LeBellier/LEDTable/Electronique/Modeling/WemosSize.jpg

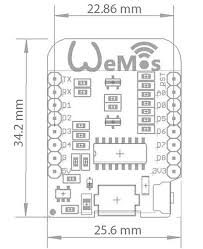
Electronique/Modeling/WemosSize.jpg
