LeBellier/LEDTable/Photos/2016-08-09 19.20.28.jpg

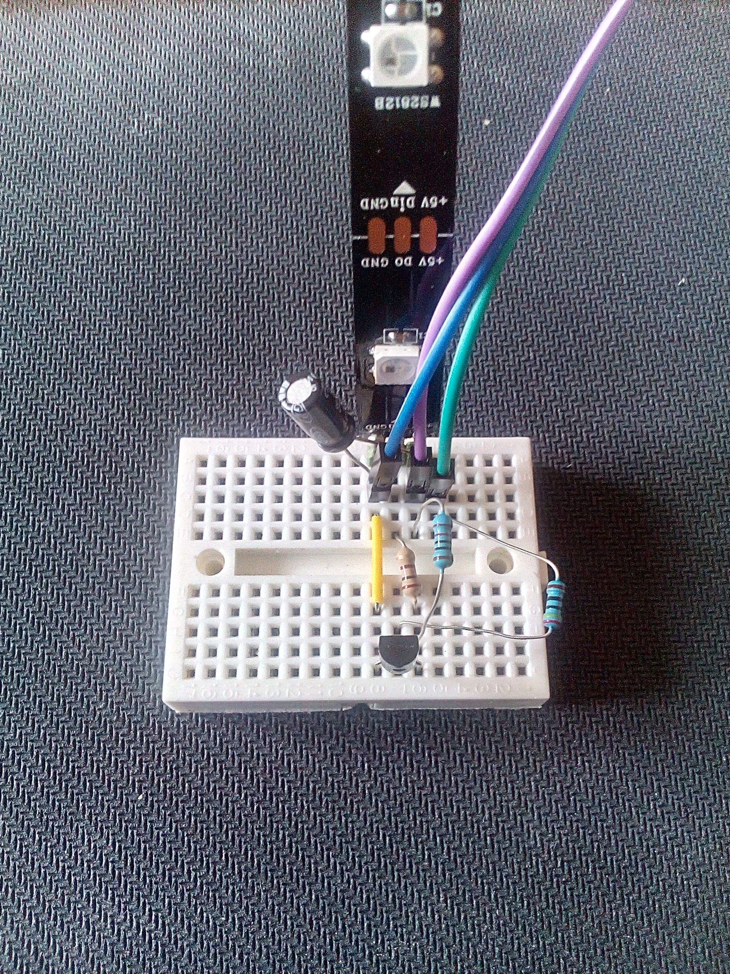
Photos/2016-08-09 19.20.28.jpg
