LeBellier/LEDTable/Photos/2016-08-09 19.20.53.jpg

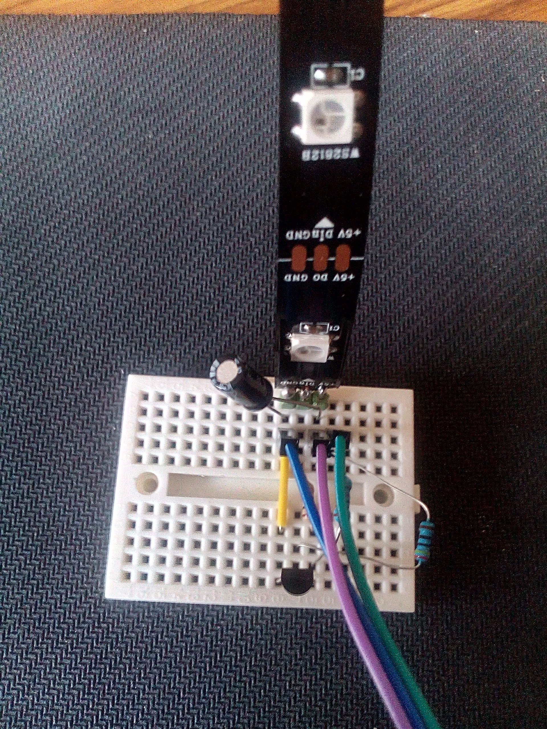
Photos/2016-08-09 19.20.53.jpg
