LeBellier/LEDTable/Photos/2016-09-05 17.38.15 Last.jpg

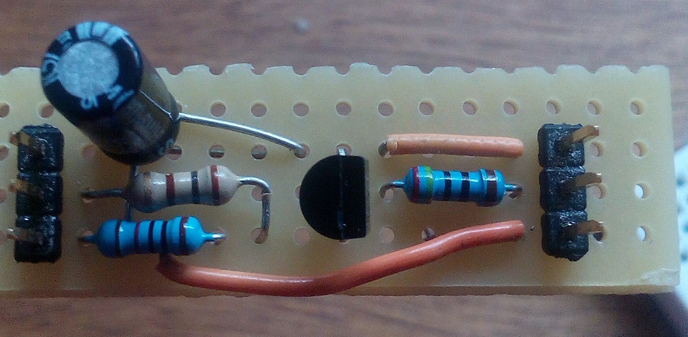
Photos/2016-09-05 17.38.15 Last.jpg
