LeBellier/LEDTable/Photos/2016-09-08 schem.png

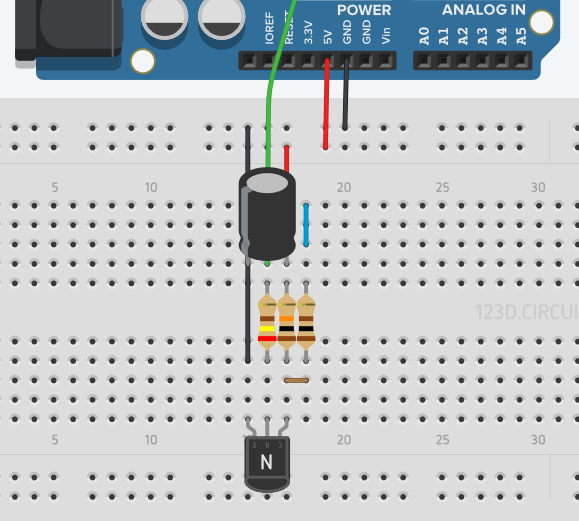
Photos/2016-09-08 schem.png
