LeBellier/LEDTable/Photos/2016-09-18 16.33.44.jpg

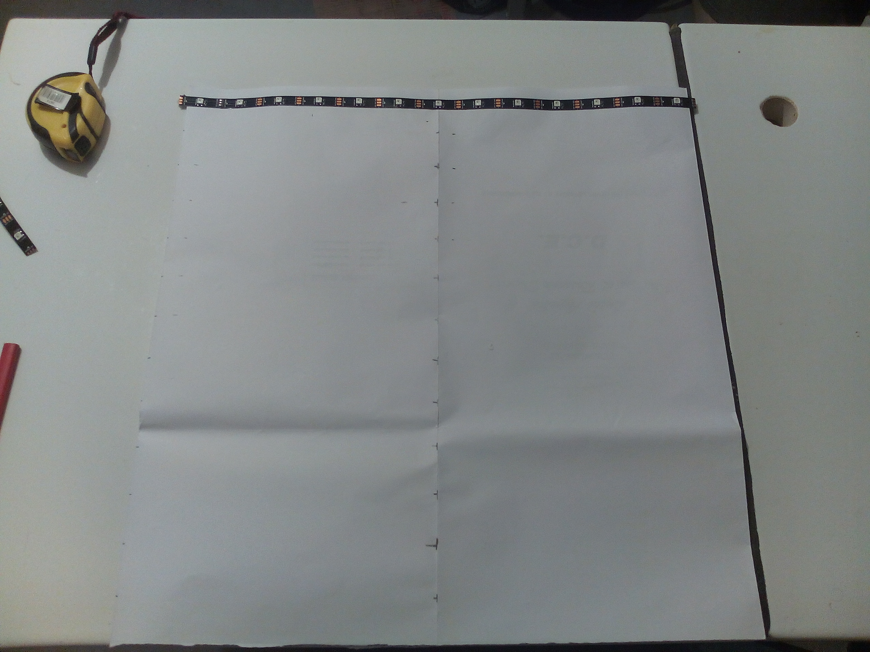
Photos/2016-09-18 16.33.44.jpg
