LeBellier/LEDTable/Photos/2016-09-18 17.44.51.jpg

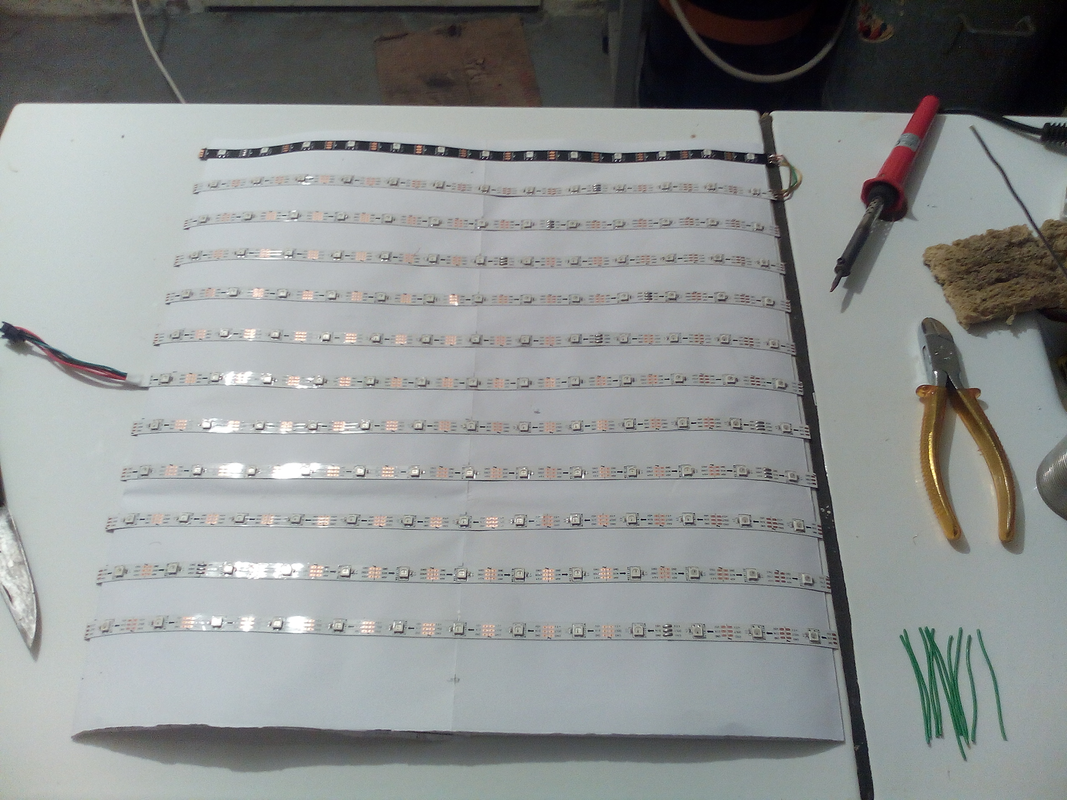
Photos/2016-09-18 17.44.51.jpg
