LeBellier/LEDTable/Photos/2016-09-18 17.50.01.jpg

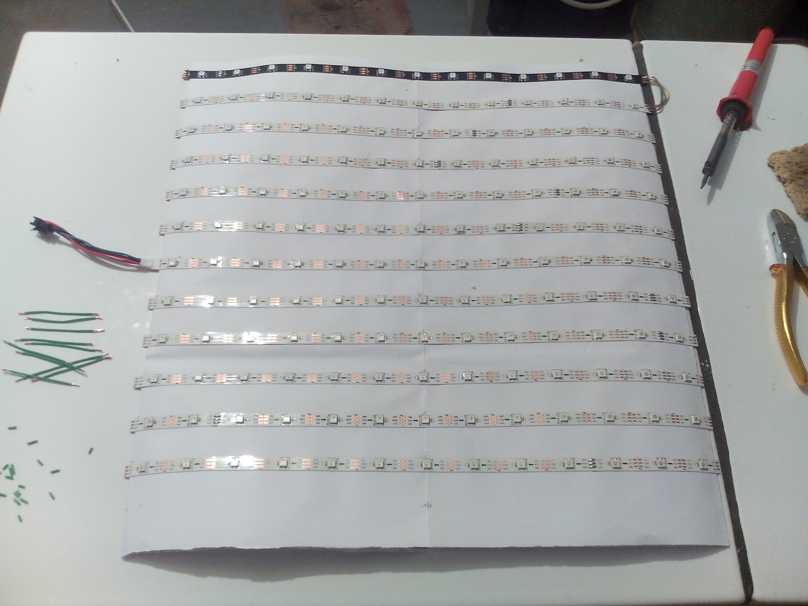
Photos/2016-09-18 17.50.01.jpg
