LeBellier/LEDTable/Photos/2016-09-18 18.18.31.jpg

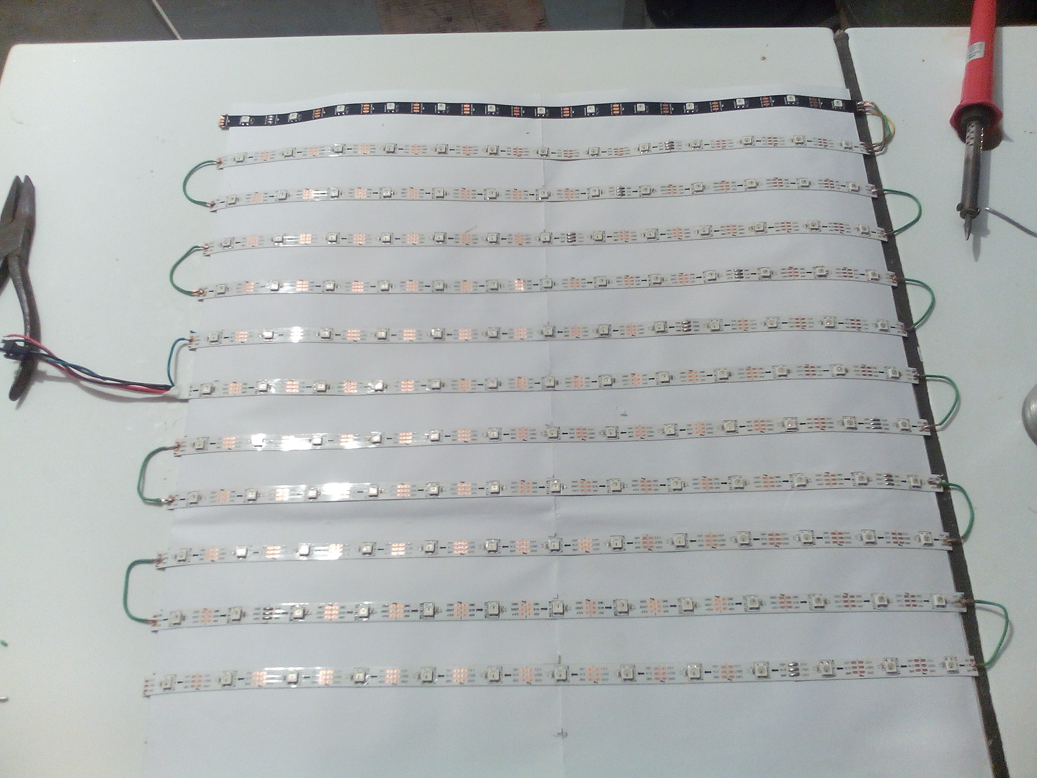
Photos/2016-09-18 18.18.31.jpg
