LeBellier/LEDTable/Photos/2016-09-18 19.18.12.jpg

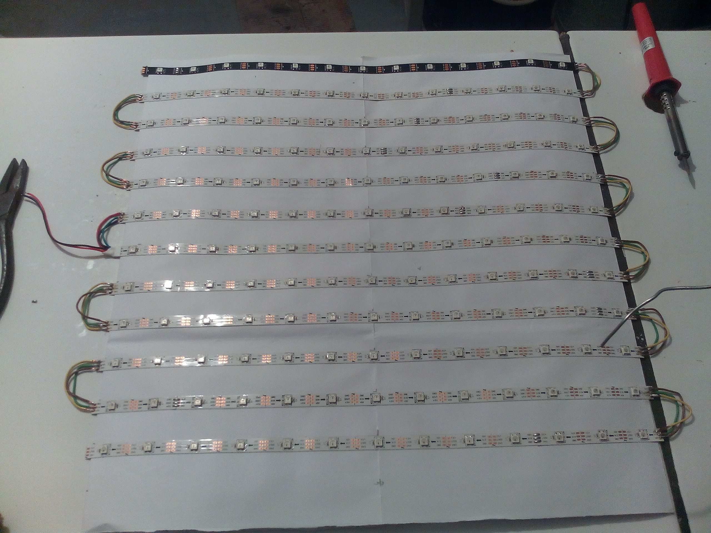
Photos/2016-09-18 19.18.12.jpg
