LeBellier/LEDTable/Photos/2016-09-18 19.18.13.jpg

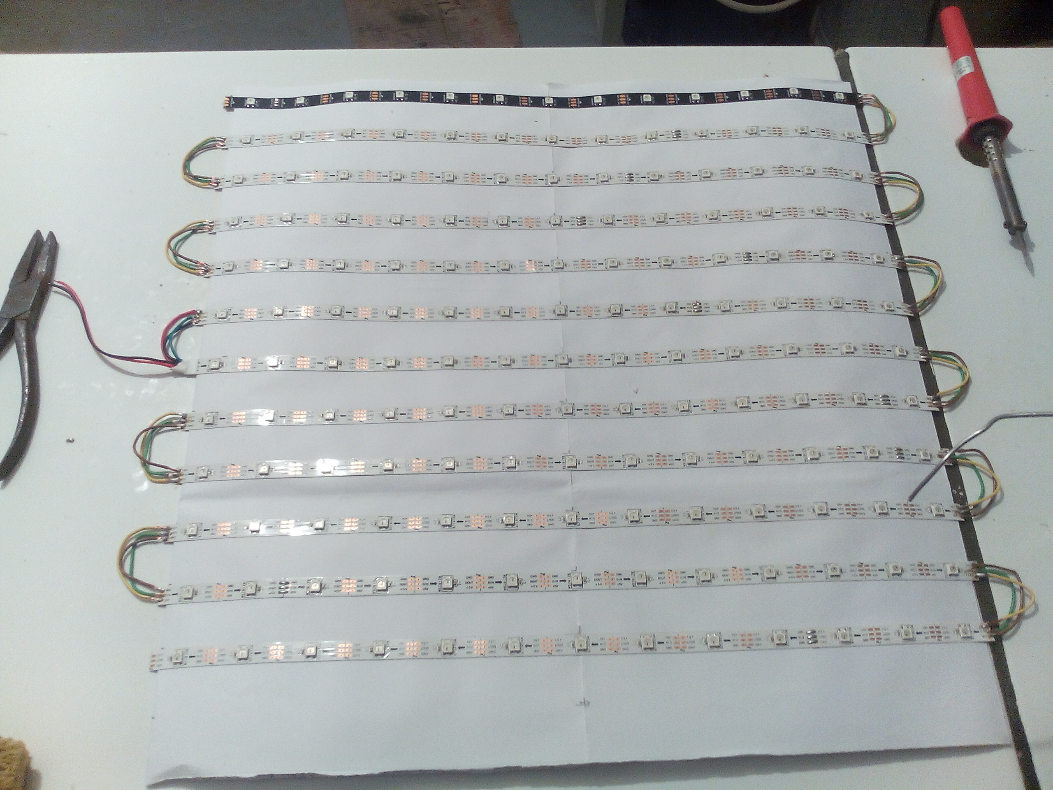
Photos/2016-09-18 19.18.13.jpg
