LeBellier/LEDTable/Photos/2016-09-18 19.37.42.jpg

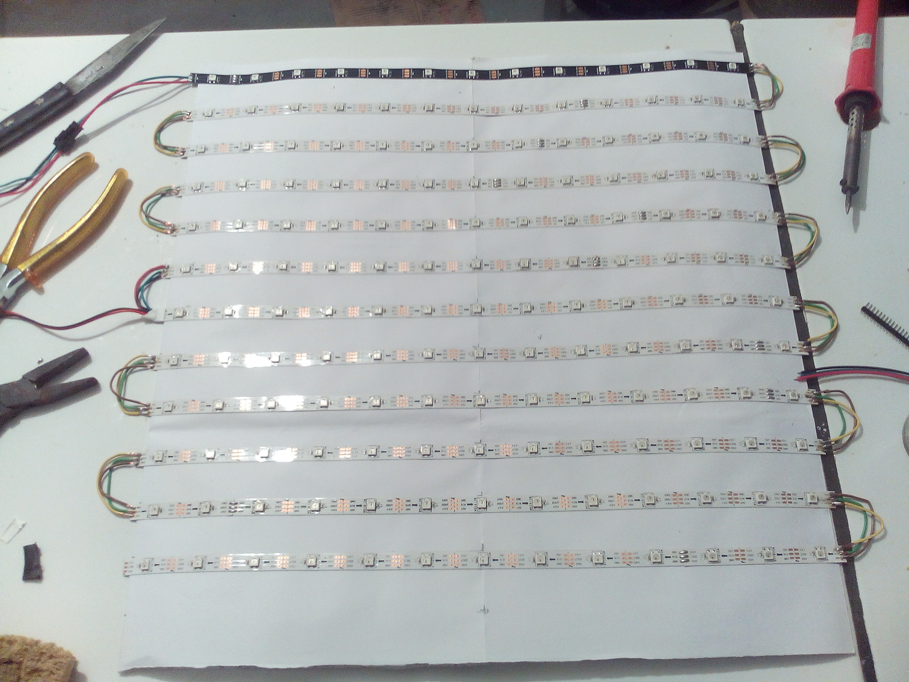
Photos/2016-09-18 19.37.42.jpg
