LeBellier/LEDTable/Photos/2016-09-19 10.16.02.jpg

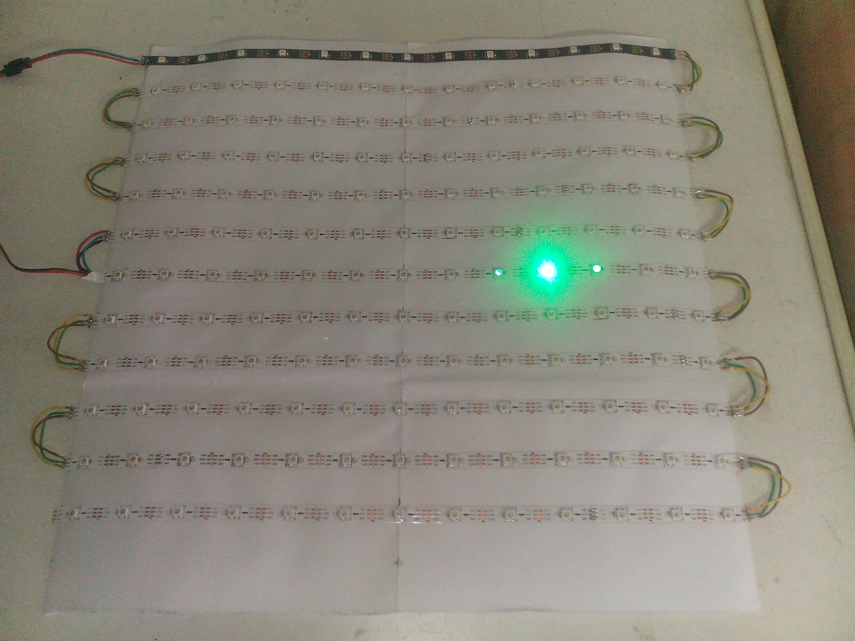
Photos/2016-09-19 10.16.02.jpg
