LeBellier/LEDTable/Photos/2016-09-22 15.28.25.jpg

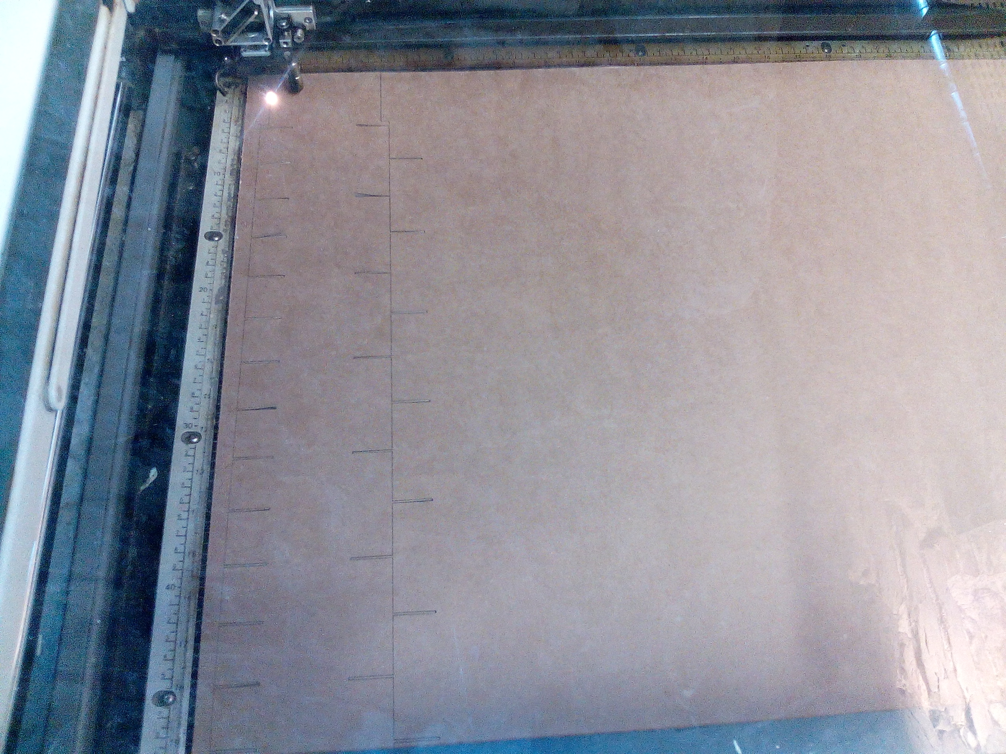
Photos/2016-09-22 15.28.25.jpg
