LeBellier/LEDTable/Photos/2016-09-22 15.30.50.jpg

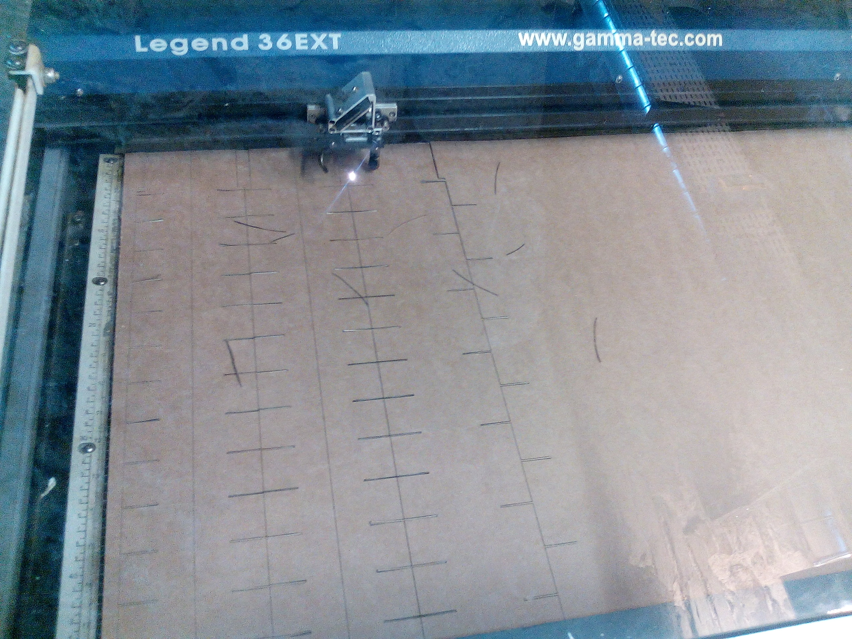
Photos/2016-09-22 15.30.50.jpg
