LeBellier/LEDTable/Photos/2016-09-26 12.01.59.jpg

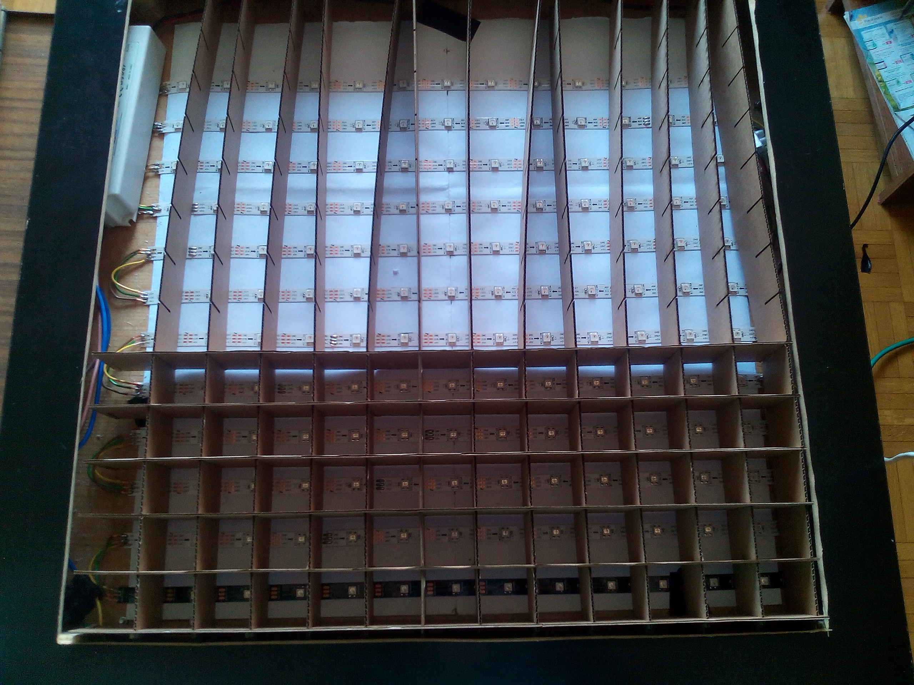
Photos/2016-09-26 12.01.59.jpg
