LeBellier/LEDTable/Photos/2016-09-26 12.21.53.jpg

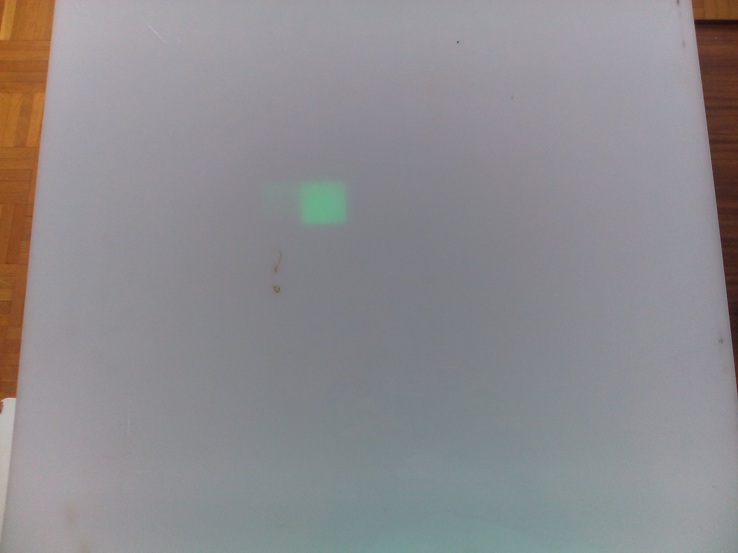
Photos/2016-09-26 12.21.53.jpg
