LeBellier/LEDTable/Photos/2016-09-26 15.10.22.jpg

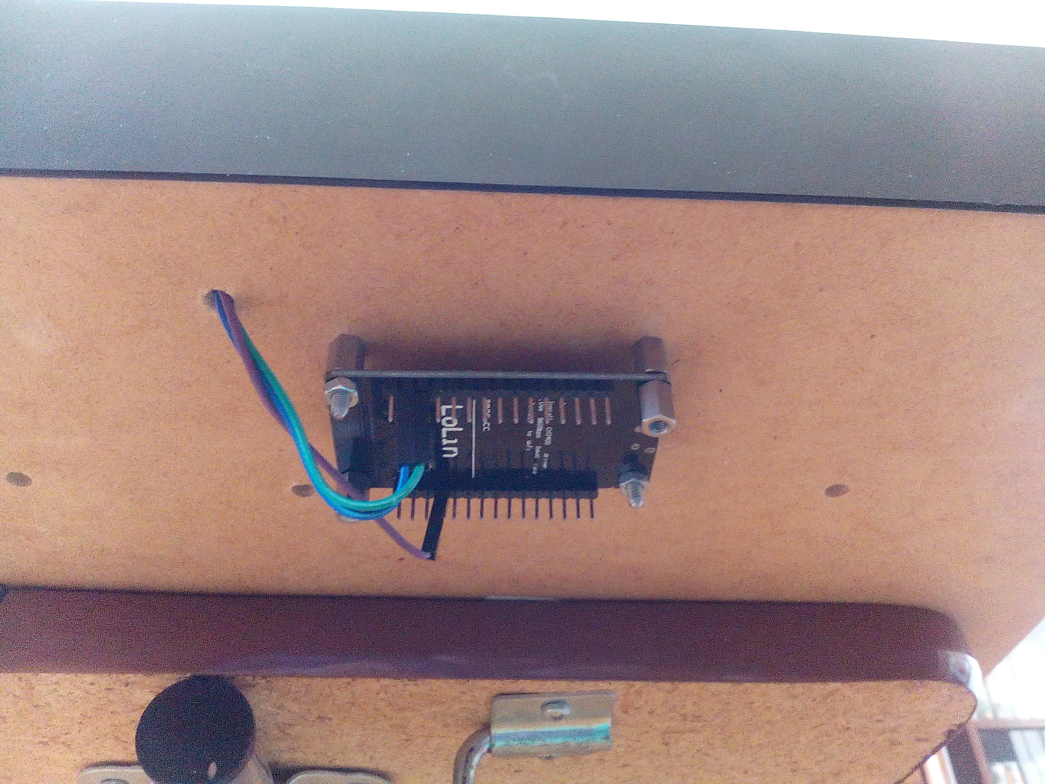
Photos/2016-09-26 15.10.22.jpg
