LeBellier/LEDTable/Photos/2016-10-25 10.06.50.jpg

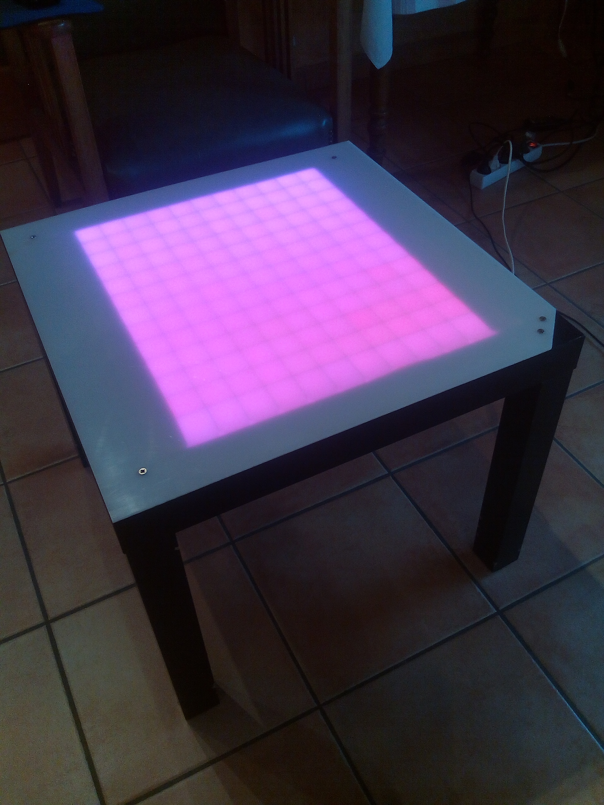
Photos/2016-10-25 10.06.50.jpg
