LeBellier/LEDTable/CodeArduino/TableALed/include/CharAndColor.h

// CharAndColor.h

#ifndef _CHARANDCOLOR_h
#define _CHARANDCOLOR_h

//Define the "Normal" 32 bit colors
static const uint32_t BLACK = 0;
static const uint32_t RED = 0xFF << 16;
static const uint32_t GREEN = 0xFF << 8;
static const uint32_t BLUE = 0xFF;
static const uint32_t ORANGE = RED | GREEN;
static const uint32_t MAGENTA = RED | BLUE;
static const uint32_t TEAL = BLUE | GREEN;
static const uint32_t WHITE = (RED | GREEN | BLUE);

//Chars
//8x8 font.
const char letters[] = { 0x00, 0x00, 0x00, 0x00, 0x00, 0x00, 0x00, 0x00, //0/ --> ' '
0x00, 0x7E, 0x11, 0x11, 0x11, 0x7E, 0x00, 0x00, //65/ --> A
0x00, 0x7F, 0x49, 0x49, 0x49, 0x36, 0x00, 0x00, //66/ --> B
0x00, 0x3E, 0x41, 0x41, 0x41, 0x22, 0x00, 0x00, //67/ --> C
0x00, 0x7F, 0x41, 0x41, 0x22, 0x1C, 0x00, 0x00, //68/ --> D
0x00, 0x7F, 0x49, 0x49, 0x49, 0x41, 0x00, 0x00, //69/ --> E
0x00, 0x7F, 0x09, 0x09, 0x09, 0x01, 0x00, 0x00, //70/ --> F
0x00, 0x3E, 0x41, 0x49, 0x49, 0x3A, 0x00, 0x00, //71/ --> G
0x00, 0x7F, 0x08, 0x08, 0x08, 0x7F, 0x00, 0x00, //72/ --> H
0x00, 0x00, 0x41, 0x7F, 0x41, 0x00, 0x00, 0x00, //73/ --> I
0x00, 0x20, 0x40, 0x41, 0x3F, 0x01, 0x00, 0x00, //74/ --> J
0x00, 0x7F, 0x08, 0x14, 0x22, 0x41, 0x00, 0x00, //75/ --> K
0x00, 0x7F, 0x40, 0x40, 0x40, 0x40, 0x00, 0x00, //76/ --> L
0x00, 0x7F, 0x02, 0x0C, 0x02, 0x7F, 0x00, 0x00, //77/ --> M
0x00, 0x7F, 0x04, 0x08, 0x10, 0x7F, 0x00, 0x00, //78/ --> N
0x00, 0x3E, 0x41, 0x41, 0x41, 0x3E, 0x00, 0x00, //79/ --> O
0x00, 0x7F, 0x09, 0x09, 0x09, 0x06, 0x00, 0x00, //80/ --> P
0x3E, 0x41, 0x51, 0x21, 0x5E, 0x00, 0x00, 0x00, //81/ --> Q
0x00, 0x7F, 0x09, 0x19, 0x29, 0x46, 0x00, 0x00, //82/ --> R
0x00, 0x46, 0x49, 0x49, 0x49, 0x31, 0x00, 0x00, //83/ --> S
0x00, 0x01, 0x01, 0x7F, 0x01, 0x01, 0x00, 0x00, //84/ --> T
0x00, 0x3F, 0x40, 0x40, 0x40, 0x3F, 0x00, 0x00, //85/ --> U
0x00, 0x1F, 0x20, 0x40, 0x20, 0x1F, 0x00, 0x00, //86/ --> V
0x00, 0x3F, 0x40, 0x70, 0x40, 0x3F, 0x00, 0x00, //87/ --> W
0x00, 0x63, 0x14, 0x08, 0x14, 0x63, 0x00, 0x00, //88/ --> X
0x00, 0x07, 0x08, 0x70, 0x08, 0x07, 0x00, 0x00, //89/ --> Y
0x00, 0x61, 0x51, 0x49, 0x45, 0x43, 0x00, 0x00, //90/ --> Z
};
//Font 3*6
const char numbers[] = { 0x00, 0x00, 0x00, //0 -->" "
0x1F, 0x11, 0x1F, //48-->0
0x00, 0x1F, 0x00, //49-->1
0x17, 0x15, 0x1D, //50-->2
0x11, 0x15, 0x1F, //51-->3
0x1E, 0x02, 0x07, //52-->4
0x1D, 0x15, 0x17, //53-->5
0x1F, 0x15, 0x07, //54-->6
0x10, 0x10, 0x1F, //55-->7
0x1F, 0x15, 0x1F, //56-->8
0x1C, 0x15, 0x1F //57-->9
};
#endif
