LeBellier/LEDTable/CodeArduino/TableALed/include/GlobalVars.h

#ifndef GLOBALVARS_H
#define GLOBALVARS_H

// Debug Speed
#define BAUDRATE 115200

// Pins and HardWare
#define pixelPin D3
#define led D4
uint8_t nbRows = 12;
uint8_t nbColumns = 13;

// Globals Object
ArtnetWifi artnet;


//Page de commentaires divers

/*#define D0   16
#define D1   5
#define D2   4
#define D3   0
#define D4   2 // builtin LED
#define D5   14
#define D6   12
#define D7   13
#define D8   15
#define D9   3
#define D10  1
*/

#endif
