LeBellier/LEDTable/CodeArduino/TableALed/include/TAL.h

/*
* tal.h
*
*  Created on: 5 sept. 2017
*      Author: Bruno
*/

#ifndef TAL_H_
#define TAL_H_

#include <ArduinoOTA.h>
#include <WiFiUdp.h>
#include <WiFiServer.h>
#include <WiFiClientSecure.h>
#include <WiFiClient.h>
#include <ESP8266WiFiType.h>
#include <ESP8266WiFiSTA.h>
#include <ESP8266WiFiScan.h>
#include <ESP8266WiFiMulti.h>
#include <ESP8266WiFiGeneric.h>
#include <ESP8266WiFiAP.h>
#include <ESP8266WiFi.h>
#include <DNSServer.h>
#include <ESP8266WebServer.h>

#include <Adafruit_NeoPixel.h>
#include "MatrixStrip.h"
#include "ServerManager.h"
#include "WifiManager.h"

#include <ESP8266WebServer.h>
#include "MatrixStrip.h"
#include "ESP8266TelnetServer.h"
#include "ServerManager.h"
#include "WifiManager.h"
#include <ArtnetWifi.h>

#include "GlobalVars.h"

#include "Animations.h" // besoin de IPAdress
#include "Callbacks.h"	// besoin du strip

#endif /* TAL_H_ */
