LeBellier/LEDTable/CodeArduino/FTPServerSample/FTPServerSample.ino

#include <ESP8266WiFi.h>          //https://github.com/esp8266/Arduino

//needed for library
#include <DNSServer.h>
#include <ESP8266WebServer.h>
#include "WiFiManager.h"          //https://github.com/tzapu/WiFiManager

#include <ESP8266FtpServer.h>

FtpServer ftpSrv;   //set #define FTP_DEBUG in ESP8266FtpServer.h to see ftp verbose on serial

void configModeCallback (WiFiManager *myWiFiManager) {
  Serial.println("Entered config mode");
  Serial.println(WiFi.softAPIP());
  //if you used auto generated SSID, print it
  Serial.println(myWiFiManager->getConfigPortalSSID());
}


void setup(void) {
  // put your setup code here, to run once:
  Serial.begin(115200);

  //WiFiManager
  //Local intialization. Once its business is done, there is no need to keep it around
  WiFiManager wifiManager;
  //reset settings - for testing
  //wifiManager.resetSettings();

  //set callback that gets called when connecting to previous WiFi fails, and enters Access Point mode
  wifiManager.setAPCallback(configModeCallback);

  //fetches ssid and pass and tries to connect
  //if it does not connect it starts an access point with the specified name
  //here  "AutoConnectAP"
  //and goes into a blocking loop awaiting configuration
  if (!wifiManager.autoConnect()) {
    Serial.println("failed to connect and hit timeout");
    //reset and try again, or maybe put it to deep sleep
    ESP.reset();
    delay(1000);
  }

  //if you get here you have connected to the WiFi
  Serial.println("connected...yeey :)");

  /////FTP Setup, ensure SPIFFS is started before ftp;  /////////

  if (SPIFFS.begin()) {
    Serial.println("SPIFFS opened!");
    ftpSrv.begin("esp8266", "esp8266");   //username, password for ftp.  set ports in ESP8266FtpServer.h  (default 21, 50009 for PASV)
  }
}

void loop(void) {
  ftpSrv.handleFTP();        //make sure in loop you call handleFTP()!!

}
